lmarzen/esp32-weather-epd/platformio/include/_locale.h

/* Locale data declarations for esp32-weather-epd.
 * Copyright (C) 2022-2026  Luke Marzen
 *
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
 * You should have received a copy of the GNU General Public License
 * along with this program.  If not, see <https://www.gnu.org/licenses/>.
 */

#ifndef ___LOCALE_H__
#define ___LOCALE_H__

#include <vector>
#include <Arduino.h>
#include <aqi.h>

// LC_TIME
extern const char *LC_D_T_FMT;
extern const char *LC_D_FMT;
extern const char *LC_T_FMT;
extern const char *LC_T_FMT_AMPM;
extern const char *LC_AM_STR;
extern const char *LC_PM_STR;
extern const char *LC_DAY[7];
extern const char *LC_ABDAY[7];
extern const char *LC_MON[12];
extern const char *LC_ABMON[12];
extern const char *LC_ERA;
extern const char *LC_ERA_D_FMT;
extern const char *LC_ERA_D_T_FMT;
extern const char *LC_ERA_T_FMT;

// OWM LANGUAGE
extern const String OWM_LANG;

// CURRENT CONDITIONS
extern const char *TXT_FEELS_LIKE;
extern const char *TXT_SUNRISE;
extern const char *TXT_SUNSET;
extern const char *TXT_MOONRISE;
extern const char *TXT_MOONSET;
extern const char *TXT_WIND;
extern const char *TXT_HUMIDITY;
extern const char *TXT_UV_INDEX;
extern const char *TXT_PRESSURE;
extern const char *TXT_AIR_QUALITY;
extern const char *TXT_AIR_POLLUTION;
extern const char *TXT_VISIBILITY;
extern const char *TXT_INDOOR_TEMPERATURE;
extern const char *TXT_INDOOR_HUMIDITY;
extern const char *TXT_DEWPOINT;

// MOON PHASE
extern const char *TXT_MOONPHASE;
extern const char *TXT_NEW_MOON;
extern const char *TXT_WAXING_CRESCENT;
extern const char *TXT_FIRST_QUARTER;
extern const char *TXT_WAXING_GIBBOUS;
extern const char *TXT_FULL_MOON;
extern const char *TXT_WANING_GIBBOUS;
extern const char *TXT_THIRD_QUARTER;
extern const char *TXT_WANING_CRESCENT;

// UV INDEX
extern const char *TXT_UV_LOW;
extern const char *TXT_UV_MODERATE;
extern const char *TXT_UV_HIGH;
extern const char *TXT_UV_VERY_HIGH;
extern const char *TXT_UV_EXTREME;

// WIFI
extern const char *TXT_WIFI_EXCELLENT;
extern const char *TXT_WIFI_GOOD;
extern const char *TXT_WIFI_FAIR;
extern const char *TXT_WIFI_WEAK;
extern const char *TXT_WIFI_NO_CONNECTION;

// UNIT SYMBOLS - TEMPERATURE
extern const char *TXT_UNITS_TEMP_KELVIN;
extern const char *TXT_UNITS_TEMP_CELSIUS;
extern const char *TXT_UNITS_TEMP_FAHRENHEIT;
// UNIT SYMBOLS - WIND SPEED
extern const char *TXT_UNITS_SPEED_METERSPERSECOND;
extern const char *TXT_UNITS_SPEED_FEETPERSECOND;
extern const char *TXT_UNITS_SPEED_KILOMETERSPERHOUR;
extern const char *TXT_UNITS_SPEED_MILESPERHOUR;
extern const char *TXT_UNITS_SPEED_KNOTS;
extern const char *TXT_UNITS_SPEED_BEAUFORT;
// UNIT SYMBOLS - PRESSURE
extern const char *TXT_UNITS_PRES_HECTOPASCALS;
extern const char *TXT_UNITS_PRES_PASCALS;
extern const char *TXT_UNITS_PRES_MILLIMETERSOFMERCURY;
extern const char *TXT_UNITS_PRES_INCHESOFMERCURY;
extern const char *TXT_UNITS_PRES_MILLIBARS;
extern const char *TXT_UNITS_PRES_ATMOSPHERES;
extern const char *TXT_UNITS_PRES_GRAMSPERSQUARECENTIMETER;
extern const char *TXT_UNITS_PRES_POUNDSPERSQUAREINCH;
// UNIT SYMBOLS - VISIBILITY DISTANCE
extern const char *TXT_UNITS_DIST_KILOMETERS;
extern const char *TXT_UNITS_DIST_MILES;
// UNIT SYMBOLS - PRECIPITATION
extern const char *TXT_UNITS_PRECIP_MILLIMETERS;
extern const char *TXT_UNITS_PRECIP_CENTIMETERS;
extern const char *TXT_UNITS_PRECIP_INCHES;

// MISCELLANEOUS MESSAGES
// Title Case
extern const char *TXT_LOW_BATTERY;
extern const char *TXT_NETWORK_NOT_AVAILABLE;
extern const char *TXT_TIME_SYNCHRONIZATION_FAILED;
extern const char *TXT_WIFI_CONNECTION_FAILED;
// First Word Capitalized
extern const char *TXT_ATTEMPTING_HTTP_REQ;
extern const char *TXT_AWAKE_FOR;
extern const char *TXT_BATTERY_VOLTAGE;
extern const char *TXT_CONNECTING_TO;
extern const char *TXT_COULD_NOT_CONNECT_TO;
extern const char *TXT_ENTERING_DEEP_SLEEP_FOR;
extern const char *TXT_READING_FROM;
extern const char *TXT_FAILED;
extern const char *TXT_SUCCESS;
extern const char *TXT_UNKNOWN;
// All Lowercase
extern const char *TXT_NOT_FOUND;
extern const char *TXT_READ_FAILED;
// Complete 
extern const char *TXT_FAILED_TO_GET_TIME;
extern const char *TXT_HIBERNATING_INDEFINITELY_NOTICE;
extern const char *TXT_REFERENCING_OLDER_TIME_NOTICE;
extern const char *TXT_WAITING_FOR_SNTP;
extern const char *TXT_LOW_BATTERY_VOLTAGE;
extern const char *TXT_VERY_LOW_BATTERY_VOLTAGE;
extern const char *TXT_CRIT_LOW_BATTERY_VOLTAGE;

// ALERTS
extern const std::vector<String> ALERT_URGENCY;
// ALERT TERMINOLOGY
extern const std::vector<String> TERM_SMOG;
extern const std::vector<String> TERM_SMOKE;
extern const std::vector<String> TERM_FOG;
extern const std::vector<String> TERM_METEOR;
extern const std::vector<String> TERM_NUCLEAR;
extern const std::vector<String> TERM_BIOHAZARD;
extern const std::vector<String> TERM_EARTHQUAKE;
extern const std::vector<String> TERM_FIRE;
extern const std::vector<String> TERM_HEAT;
extern const std::vector<String> TERM_WINTER;
extern const std::vector<String> TERM_TSUNAMI;
extern const std::vector<String> TERM_LIGHTNING;
extern const std::vector<String> TERM_SANDSTORM;
extern const std::vector<String> TERM_FLOOD;
extern const std::vector<String> TERM_VOLCANO;
extern const std::vector<String> TERM_AIR_QUALITY;
extern const std::vector<String> TERM_TORNADO;
extern const std::vector<String> TERM_SMALL_CRAFT_ADVISORY;
extern const std::vector<String> TERM_GALE_WARNING;
extern const std::vector<String> TERM_STORM_WARNING;
extern const std::vector<String> TERM_HURRICANE_WARNING;
extern const std::vector<String> TERM_HURRICANE;
extern const std::vector<String> TERM_DUST;
extern const std::vector<String> TERM_STRONG_WIND;

// AIR QUALITY INDEX
extern "C" {
extern const aqi_scale_t AQI_SCALE;
extern const char *AUSTRALIA_AQI_TXT[6];
extern const char *CANADA_AQHI_TXT[4];
extern const char *EUROPEAN_UNION_CAQI_TXT[5];
extern const char *HONG_KONG_AQHI_TXT[5];
extern const char *INDIA_AQI_TXT[6];
extern const char *CHINA_AQI_TXT[6];
extern const char *SINGAPORE_PSI_TXT[5];
extern const char *SOUTH_KOREA_CAI_TXT[4];
extern const char *UNITED_KINGDOM_DAQI_TXT[4];
extern const char *UNITED_STATES_AQI_TXT[6];
}

// COMPASS POINT
extern const char *COMPASS_POINT_NOTATION[32];

// HTTP CLIENT ERRORS
extern const char *TXT_HTTPC_ERROR_CONNECTION_REFUSED;
extern const char *TXT_HTTPC_ERROR_SEND_HEADER_FAILED;
extern const char *TXT_HTTPC_ERROR_SEND_PAYLOAD_FAILED;
extern const char *TXT_HTTPC_ERROR_NOT_CONNECTED;
extern const char *TXT_HTTPC_ERROR_CONNECTION_LOST;
extern const char *TXT_HTTPC_ERROR_NO_STREAM;
extern const char *TXT_HTTPC_ERROR_NO_HTTP_SERVER;
extern const char *TXT_HTTPC_ERROR_TOO_LESS_RAM;
extern const char *TXT_HTTPC_ERROR_ENCODING;
extern const char *TXT_HTTPC_ERROR_STREAM_WRITE;
extern const char *TXT_HTTPC_ERROR_READ_TIMEOUT;

// HTTP RESPONSE STATUS CODES
// 1xx - Informational Responses
extern const char *TXT_HTTP_RESPONSE_100;
extern const char *TXT_HTTP_RESPONSE_101;
extern const char *TXT_HTTP_RESPONSE_102;
extern const char *TXT_HTTP_RESPONSE_103;
// 2xx - Successful Responses
extern const char *TXT_HTTP_RESPONSE_200;
extern const char *TXT_HTTP_RESPONSE_201;
extern const char *TXT_HTTP_RESPONSE_202;
extern const char *TXT_HTTP_RESPONSE_203;
extern const char *TXT_HTTP_RESPONSE_204;
extern const char *TXT_HTTP_RESPONSE_205;
extern const char *TXT_HTTP_RESPONSE_206;
extern const char *TXT_HTTP_RESPONSE_207;
extern const char *TXT_HTTP_RESPONSE_208;
extern const char *TXT_HTTP_RESPONSE_226;
// 3xx - Redirection Responses
extern const char *TXT_HTTP_RESPONSE_300;
extern const char *TXT_HTTP_RESPONSE_301;
extern const char *TXT_HTTP_RESPONSE_302;
extern const char *TXT_HTTP_RESPONSE_303;
extern const char *TXT_HTTP_RESPONSE_304;
extern const char *TXT_HTTP_RESPONSE_305;
extern const char *TXT_HTTP_RESPONSE_307;
extern const char *TXT_HTTP_RESPONSE_308;
// 4xx - Client Error Responses
extern const char *TXT_HTTP_RESPONSE_400;
extern const char *TXT_HTTP_RESPONSE_401;
extern const char *TXT_HTTP_RESPONSE_402;
extern const char *TXT_HTTP_RESPONSE_403;
extern const char *TXT_HTTP_RESPONSE_404;
extern const char *TXT_HTTP_RESPONSE_405;
extern const char *TXT_HTTP_RESPONSE_406;
extern const char *TXT_HTTP_RESPONSE_407;
extern const char *TXT_HTTP_RESPONSE_408;
extern const char *TXT_HTTP_RESPONSE_409;
extern const char *TXT_HTTP_RESPONSE_410;
extern const char *TXT_HTTP_RESPONSE_411;
extern const char *TXT_HTTP_RESPONSE_412;
extern const char *TXT_HTTP_RESPONSE_413;
extern const char *TXT_HTTP_RESPONSE_414;
extern const char *TXT_HTTP_RESPONSE_415;
extern const char *TXT_HTTP_RESPONSE_416;
extern const char *TXT_HTTP_RESPONSE_417;
extern const char *TXT_HTTP_RESPONSE_418;
extern const char *TXT_HTTP_RESPONSE_421;
extern const char *TXT_HTTP_RESPONSE_422;
extern const char *TXT_HTTP_RESPONSE_423;
extern const char *TXT_HTTP_RESPONSE_424;
extern const char *TXT_HTTP_RESPONSE_425;
extern const char *TXT_HTTP_RESPONSE_426;
extern const char *TXT_HTTP_RESPONSE_428;
extern const char *TXT_HTTP_RESPONSE_429;
extern const char *TXT_HTTP_RESPONSE_431;
extern const char *TXT_HTTP_RESPONSE_451;
// 5xx - Server Error Responses
extern const char *TXT_HTTP_RESPONSE_500;
extern const char *TXT_HTTP_RESPONSE_501;
extern const char *TXT_HTTP_RESPONSE_502;
extern const char *TXT_HTTP_RESPONSE_503;
extern const char *TXT_HTTP_RESPONSE_504;
extern const char *TXT_HTTP_RESPONSE_505;
extern const char *TXT_HTTP_RESPONSE_506;
extern const char *TXT_HTTP_RESPONSE_507;
extern const char *TXT_HTTP_RESPONSE_508;
extern const char *TXT_HTTP_RESPONSE_510;
extern const char *TXT_HTTP_RESPONSE_511;

// ARDUINOJSON DESERIALIZATION ERROR CODES
extern const char *TXT_DESERIALIZATION_ERROR_OK;
extern const char *TXT_DESERIALIZATION_ERROR_EMPTY_INPUT;
extern const char *TXT_DESERIALIZATION_ERROR_INCOMPLETE_INPUT;
extern const char *TXT_DESERIALIZATION_ERROR_INVALID_INPUT;
extern const char *TXT_DESERIALIZATION_ERROR_NO_MEMORY;
extern const char *TXT_DESERIALIZATION_ERROR_TOO_DEEP;

// WIFI STATUS
extern const char *TXT_WL_NO_SHIELD;
extern const char *TXT_WL_IDLE_STATUS;
extern const char *TXT_WL_NO_SSID_AVAIL;
extern const char *TXT_WL_SCAN_COMPLETED;
extern const char *TXT_WL_CONNECTED;
extern const char *TXT_WL_CONNECT_FAILED;
extern const char *TXT_WL_CONNECTION_LOST;
extern const char *TXT_WL_DISCONNECTED;

#endif
