lmarzen/esp32-weather-epd/platformio/include/renderer.h

/* Renderer declarations for esp32-weather-epd.
 * Copyright (C) 2022-2026  Luke Marzen
 *
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
 * You should have received a copy of the GNU General Public License
 * along with this program.  If not, see <https://www.gnu.org/licenses/>.
 */

#ifndef __RENDERER_H__
#define __RENDERER_H__

#include <vector>
#include <Arduino.h>
#include <time.h>
#include "api_response.h"
#include "config.h"

#ifdef DISP_BW_V2
  #define DISP_WIDTH  800
  #define DISP_HEIGHT 480
  #include <GxEPD2_BW.h>
  extern GxEPD2_BW<GxEPD2_750_GDEY075T7,
                   GxEPD2_750_GDEY075T7::HEIGHT> display;
#endif
#ifdef DISP_3C_B
  #define DISP_WIDTH  800
  #define DISP_HEIGHT 480
  #include <GxEPD2_3C.h>
  extern GxEPD2_3C<GxEPD2_750c_GDEY075Z08,
                   GxEPD2_750c_GDEY075Z08::HEIGHT / 2> display;
#endif
#ifdef DISP_7C_F
  #define DISP_WIDTH  800
  #define DISP_HEIGHT 480
  #include <GxEPD2_7C.h>
  extern GxEPD2_7C<GxEPD2_730c_GDEY073D46, 
                   GxEPD2_730c_GDEY073D46::HEIGHT / 4> display;
#endif
#ifdef DISP_BW_V1
  #define DISP_WIDTH  640
  #define DISP_HEIGHT 384
  #include <GxEPD2_BW.h>
  extern GxEPD2_BW<GxEPD2_750,
                   GxEPD2_750::HEIGHT> display;
#endif

typedef enum alignment
{
  LEFT,
  RIGHT,
  CENTER
} alignment_t;

uint16_t getStringWidth(const String &text);
uint16_t getStringHeight(const String &text);
void drawString(int16_t x, int16_t y, const String &text, alignment_t alignment,
                uint16_t color=GxEPD_BLACK);
void drawMultiLnString(int16_t x, int16_t y, const String &text,
                       alignment_t alignment, uint16_t max_width,
                       uint16_t max_lines, int16_t line_spacing,
                       uint16_t color=GxEPD_BLACK);
void initDisplay();
void powerOffDisplay();
void drawCurrentConditions(const owm_current_t &current,
                           const owm_daily_t &today,
                           const owm_resp_air_pollution_t &owm_air_pollution,
                           float inTemp, float inHumidity);
void drawForecast(const owm_daily_t *daily, tm timeInfo);
void drawAlerts(std::vector<owm_alerts_t> &alerts,
                const String &city, const String &date);
void drawLocationDate(const String &city, const String &date);
void drawOutlookGraph(const owm_hourly_t *hourly, const owm_daily_t *daily,
                      tm timeInfo);
void drawStatusBar(const String &statusStr, const String &refreshTimeStr,
                   int rssi, uint32_t batVoltage);
void drawError(const uint8_t *bitmap_196x196,
               const String &errMsgLn1, const String &errMsgLn2="");
void drawCurrentSunrise(const owm_current_t &current);
void drawCurrentSunset(const owm_current_t &current);
void drawCurrentInTemp(float inTemp);
void drawCurrentInHumidity(float inHumidity);
void drawCurrentMoonrise(const owm_daily_t &today);
void drawCurrentMoonset(const owm_daily_t &today);
void drawCurrentWind(const owm_current_t &current);
void drawCurrentHumidity(const owm_current_t &current);
void drawCurrentUVI(const owm_current_t &current);
void drawCurrentPressure(const owm_current_t &current);
void drawCurrentVisibility(const owm_current_t &current);
void drawCurrentAirQuality(const owm_resp_air_pollution_t &owm_air_pollution);
void drawCurrentMoonphase(const owm_daily_t &today);
void drawCurrentDewpoint(const owm_current_t &current);

#endif
