lmarzen/esp32-weather-epd/platformio/include/display_utils.h

/* Display helper utility declarations for esp32-weather-epd.
 * Copyright (C) 2022-2026  Luke Marzen
 *
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
 * You should have received a copy of the GNU General Public License
 * along with this program.  If not, see <https://www.gnu.org/licenses/>.
 */

#ifndef __DISPLAY_UTILS_H__
#define __DISPLAY_UTILS_H__

#include <vector>
#include <time.h>
#include "api_response.h"

enum alert_category {
  NOT_FOUND = -1,
  SMOG,
  SMOKE,
  FOG,
  METEOR,
  NUCLEAR,
  BIOHAZARD,
  EARTHQUAKE,
  FIRE,
  HEAT,
  WINTER,
  TSUNAMI,
  LIGHTNING,
  SANDSTORM,
  FLOOD,
  VOLCANO,
  AIR_QUALITY,
  TORNADO,
  SMALL_CRAFT_ADVISORY,
  GALE_WARNING,
  STORM_WARNING,
  HURRICANE_WARNING,
  HURRICANE,
  DUST,
  STRONG_WIND
};

uint32_t readBatteryVoltage();
uint32_t calcBatPercent(uint32_t v, uint32_t minv, uint32_t maxv);
const uint8_t *getBatBitmap24(uint32_t batPercent);
void getDateStr(String &s, tm *timeInfo);
void getRefreshTimeStr(String &s, bool timeSuccess, tm *timeInfo);
void toTitleCase(String &text);
void truncateExtraAlertInfo(String &text);
void filterAlerts(std::vector<owm_alerts_t> &resp, int *ignore_list);
const char *getUVIdesc(unsigned int uvi);
float getAvgConc(const float pollutant[], int hours);
int getAQI(const owm_resp_air_pollution_t &p);
const char *getAQIdesc(int aqi);
const char *getWiFidesc(int rssi);
const uint8_t *getWiFiBitmap16(int rssi);
const uint8_t *getHourlyForecastBitmap32(const owm_hourly_t &hourly,
                                         const owm_daily_t  &today);
const uint8_t *getDailyForecastBitmap64(const owm_daily_t &daily);
const uint8_t *getCurrentConditionsBitmap196(const owm_current_t &current,
                                             const owm_daily_t   &today);
const uint8_t *getAlertBitmap32(const owm_alerts_t &alert);
const uint8_t *getAlertBitmap48(const owm_alerts_t &alert);
enum alert_category getAlertCategory(const owm_alerts_t &alert);
const uint8_t *getWindBitmap24(int windDeg);
const char *getCompassPointNotation(int windDeg);
const char *getHttpResponsePhrase(int code);
const char *getWifiStatusPhrase(wl_status_t status);
void printHeapUsage();
void disableBuiltinLED();
const uint8_t *getMoonPhaseBitmap48(const owm_daily_t &daily);
const char *getMoonPhaseStr(const owm_daily_t &daily);

#endif
